jssting/ArduinoTec-Pedals/ArduinoTec-Pedals/confOptions.h

//confOptions.h
//debug options
#define Enable_Debug false
#define Debug_Thr true
#define Debug_Cth false
#define Debug_Brk false

// Input Precision
#define use_Dual_Thr false
#define use_Dual_Cl  false
#define use_Dual_Brk false

// initial Deadzone
#define brake_L_DZ 5
#define throttle_L_DZ 5
#define clutch_L_DZ 5

// maximum Deadzone
#define brake_U_DZ 5
#define throttle_U_DZ 5
#define clutch_U_DZ 5
